espee77/Genius-GM6000-BLE-Mouse-Revival/V1.0/3D files/Step214/Genius_GM-6000_Switch_SS-12D07-VG-4-NS-GA-PA_V0.1.stp

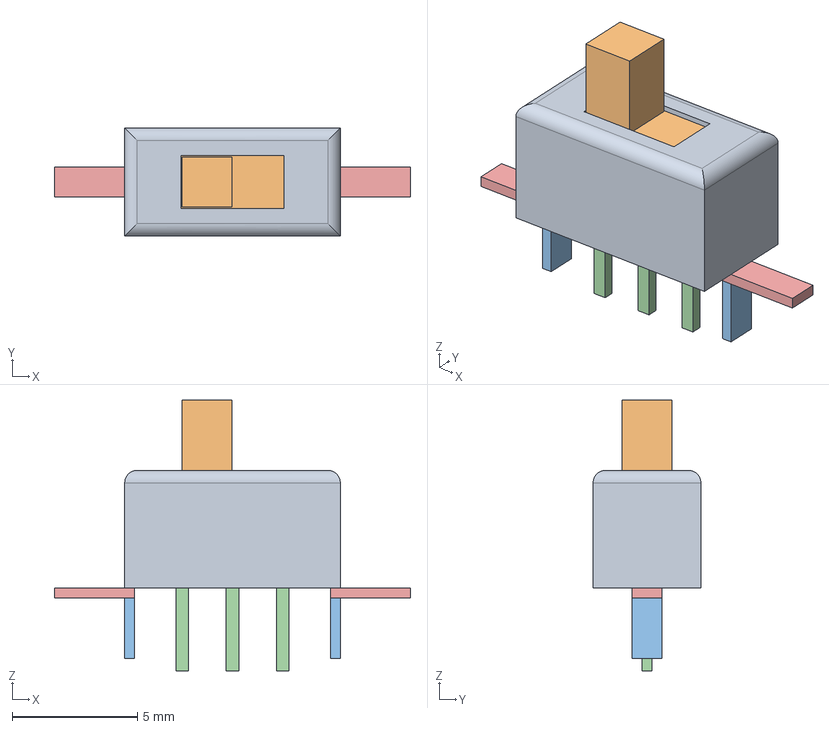
[picture p15: CAD file, 2026-07-31, an earlier design]
V1.0/3D files/Step214/Genius_GM-6000_Switch_SS-12D07-VG-4-NS-GA-PA_V0.1.stp
14.2 x 4.30 x 10.8 mm
