espee77/Genius-GM6000-BLE-Mouse-Revival/V1.01/Firmware/src/MouseOutput.h

#pragma once
#include <Arduino.h>
#include "MouseReport.h"

void mouseOutputBegin();
void mouseOutputUpdate();
bool mouseOutputConnected();
bool mouseOutputCanSend();
void mouseOutputSendReport(const MouseReportData &report);
