espee77/Genius-GM6000-BLE-Mouse-Revival/V1.01/Firmware/src/UsbMouse.h

#pragma once
#include <Arduino.h>
#include "MouseReport.h"

void usbMouseBegin();
void usbMouseUpdate();
bool usbMouseHostMounted();
bool usbMouseModeChanged();
bool usbMouseTrySendReport(const MouseReportData &report);
